Gekkio/moca-hcho/fw/build.rs

// SPDX-FileCopyrightText: 2021-2022 Joonas Javanainen <joonas.javanainen@gmail.com>
//
// SPDX-License-Identifier: MIT OR Apache-2.0

use std::env;
use std::fs::File;
use std::io::Write;
use std::path::PathBuf;

fn main() {
    let out = &PathBuf::from(env::var_os("OUT_DIR").unwrap());
    File::create(out.join("memory.x"))
        .unwrap()
        .write_all(include_bytes!("memory.x"))
        .unwrap();
    println!("cargo:rustc-link-search={}", out.display());

    println!("cargo:rerun-if-changed=memory.x");

    println!("cargo:rustc-link-arg-bins=--nmagic");
    println!("cargo:rustc-link-arg-bins=-Tlink.x");
    println!("cargo:rustc-link-arg-bins=-Tdefmt.x");
}
